snu-quiqcl/EEM2TTL/EEM2TTLv1_1/EEM2TTL-PSpiceFiles/TOP/PowerTest/PowerTest.cir

** Profile: "TOP-PowerTest"  [ C:\Jeonghyun\Lab\EEM2TTL5\EEM2TTL-PSpiceFiles\TOP\PowerTest.sim ] 

** Creating circuit file "PowerTest.cir" 
** WARNING: THIS AUTOMATICALLY GENERATED FILE MAY BE OVERWRITTEN BY SUBSEQUENT SIMULATIONS

*Libraries: 
* Profile Libraries :
* Local Libraries :
* From [PSPICE NETLIST] section of C:\SPB_DATA\cdssetup\OrCAD_PSpice\23.1.0\PSpice.ini file:
.lib "nom.lib" 

*Analysis directives: 
.TRAN  0 1000ns 0 
.OPTIONS ADVCONV
.PROBE64 V(alias(*)) I(alias(*)) W(alias(*)) D(alias(*)) NOISE(alias(*)) 
.INC "..\TOP.net" 


.END
